SteveMayze/TL2C/doc/web/image/Level-Illuminated-sm.png

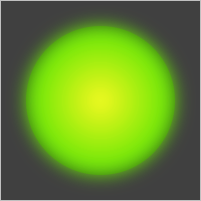
doc/web/image/Level-Illuminated-sm.png
