SteveMayze/TL2C/doc/Connection.png

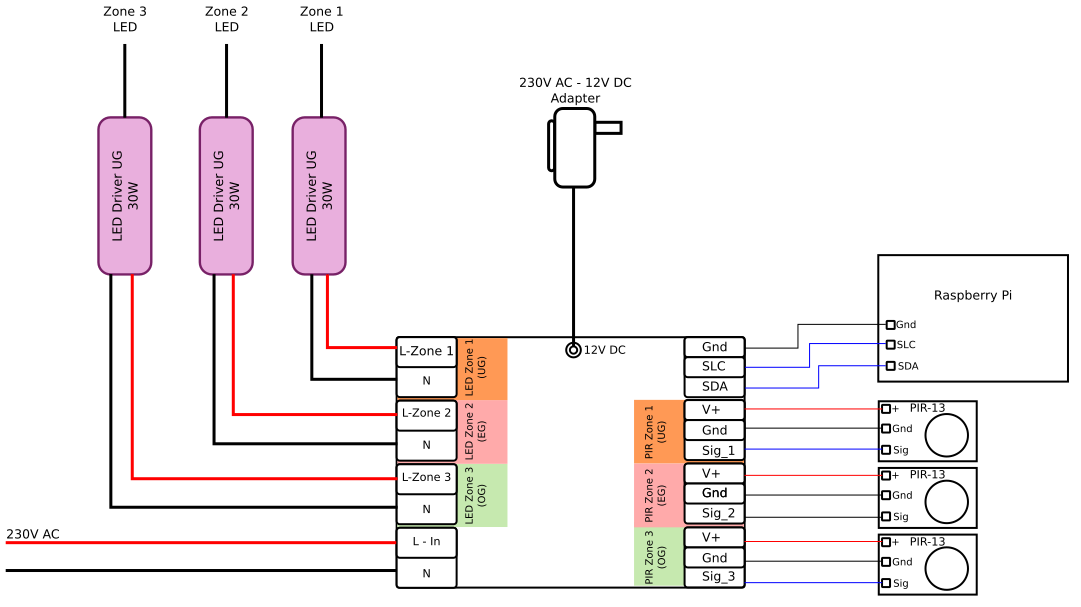
doc/Connection.png
