SteveMayze/TL2C/doc/esp32/CNMB_3_KIT.jpg

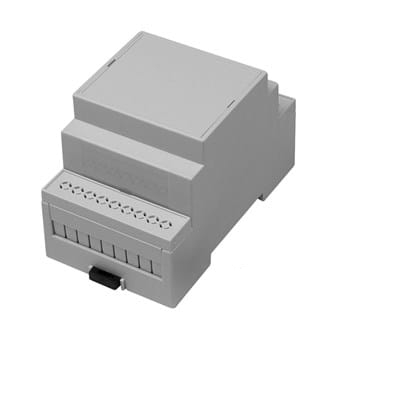
doc/esp32/CNMB_3_KIT.jpg
