SteveMayze/TL2C/doc/esp32/Layout.png

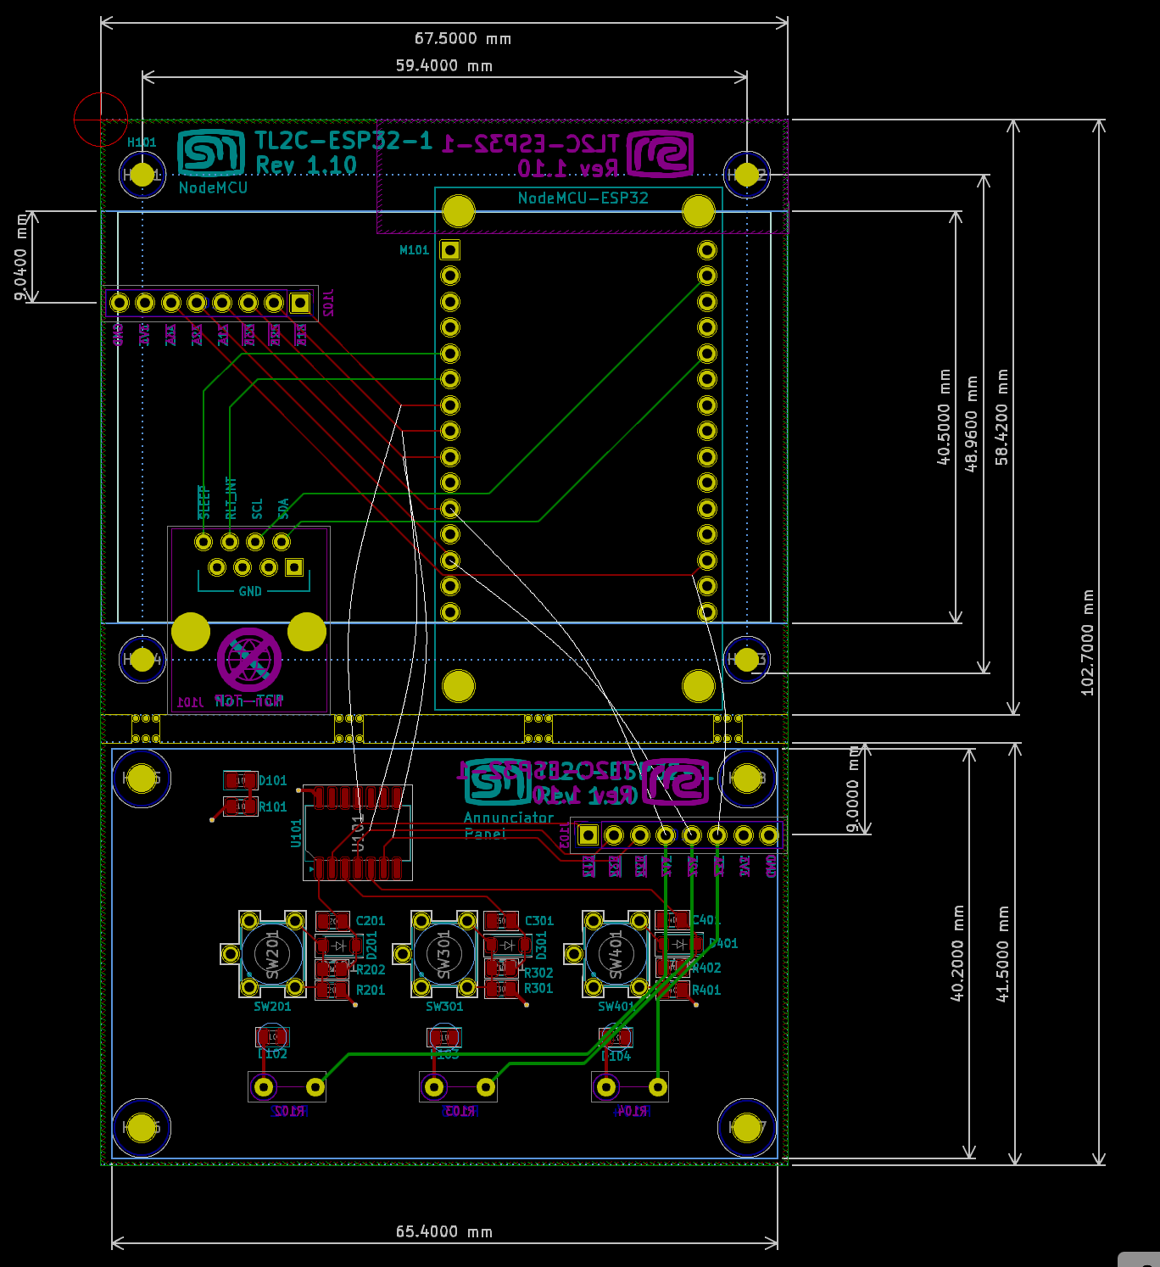
doc/esp32/Layout.png
