SteveMayze/TL2C/doc/esp32/Screenshot 2024-02-02 at 20.17.53.png

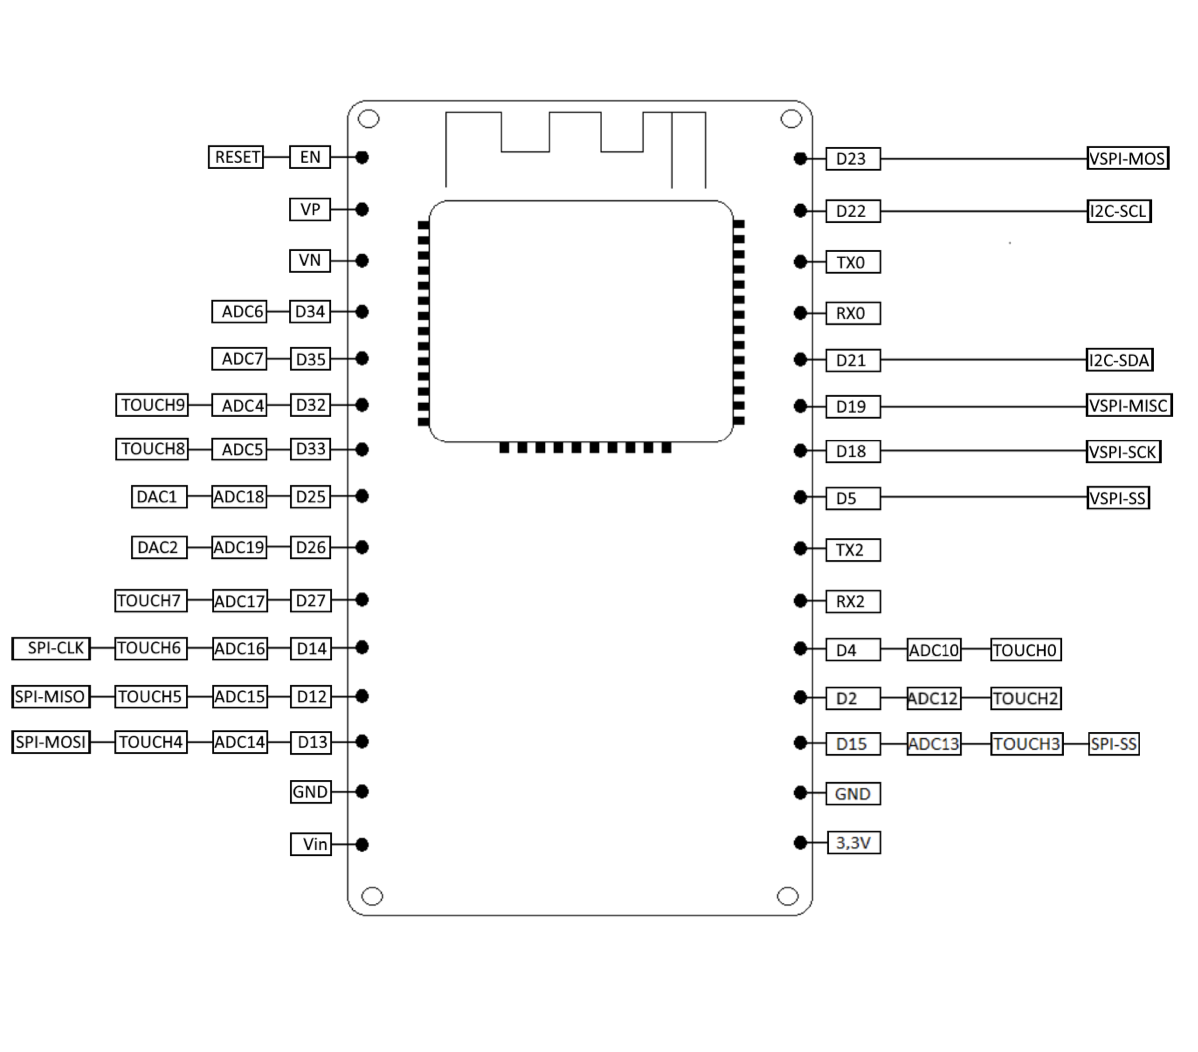
doc/esp32/Screenshot 2024-02-02 at 20.17.53.png
