SteveMayze/TL2C/doc/esp32/Screenshot 2024-02-08 at 13.55.30.png

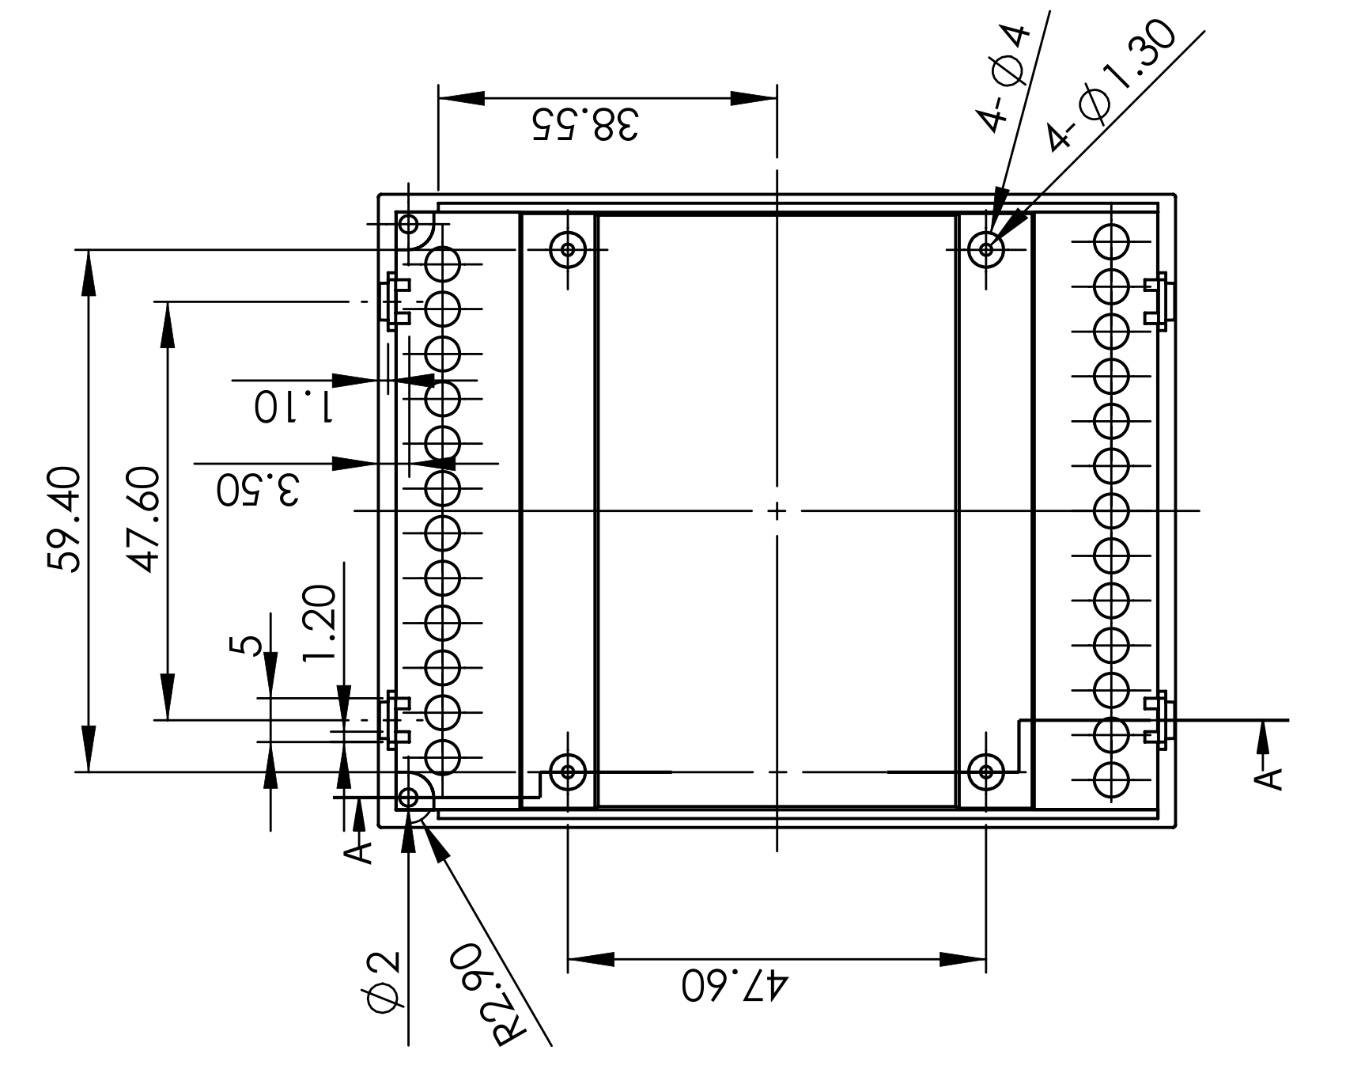
doc/esp32/Screenshot 2024-02-08 at 13.55.30.png
