SteveMayze/TL2C/doc/esp32/Screenshot 2024-03-15 at 17.32.05.png

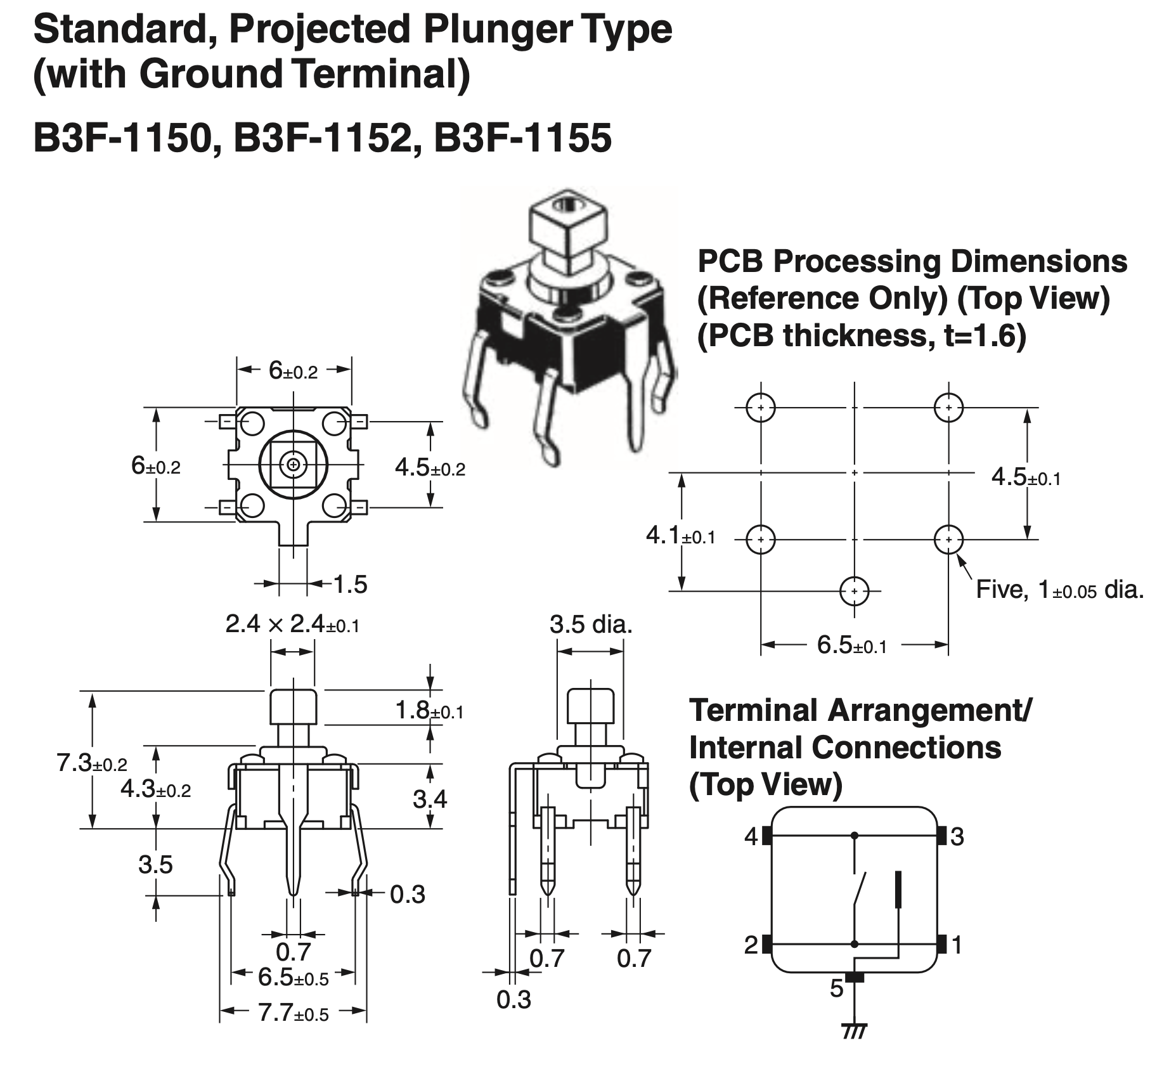
doc/esp32/Screenshot 2024-03-15 at 17.32.05.png
