SteveMayze/TL2C/doc/esp32/Screenshot 2024-03-15 at 17.46.03.png

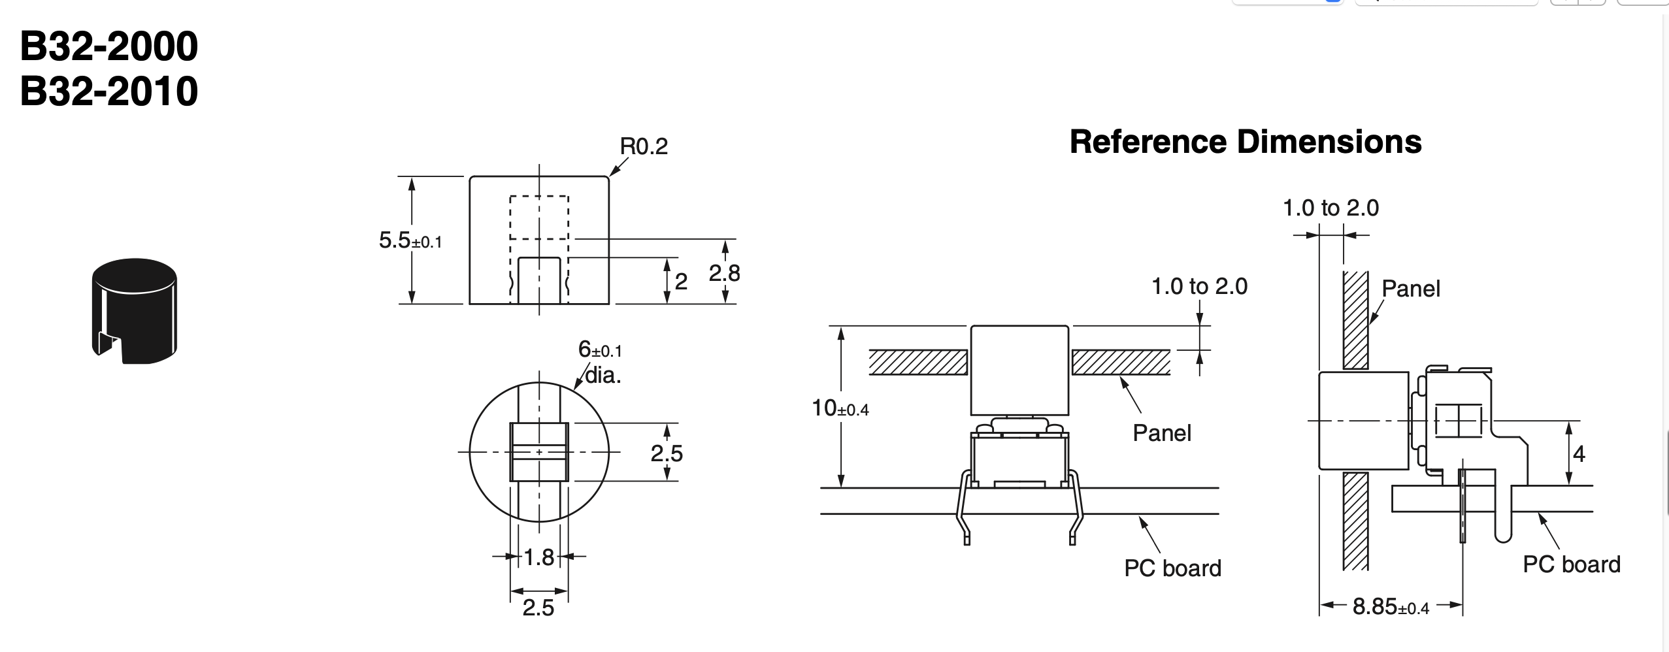
doc/esp32/Screenshot 2024-03-15 at 17.46.03.png
