SteveMayze/TL2C/doc/esp32/tl2c-esp-back.png

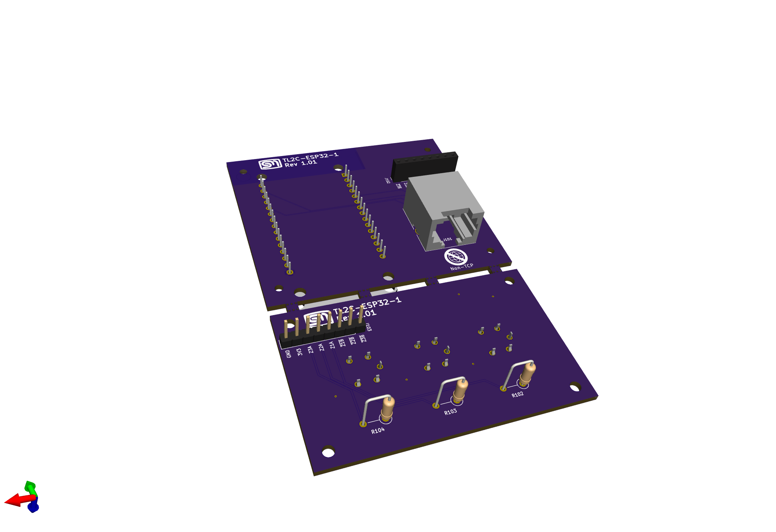
doc/esp32/tl2c-esp-back.png
