SteveMayze/TL2C/doc/esp32/tl2c-esp-front.png

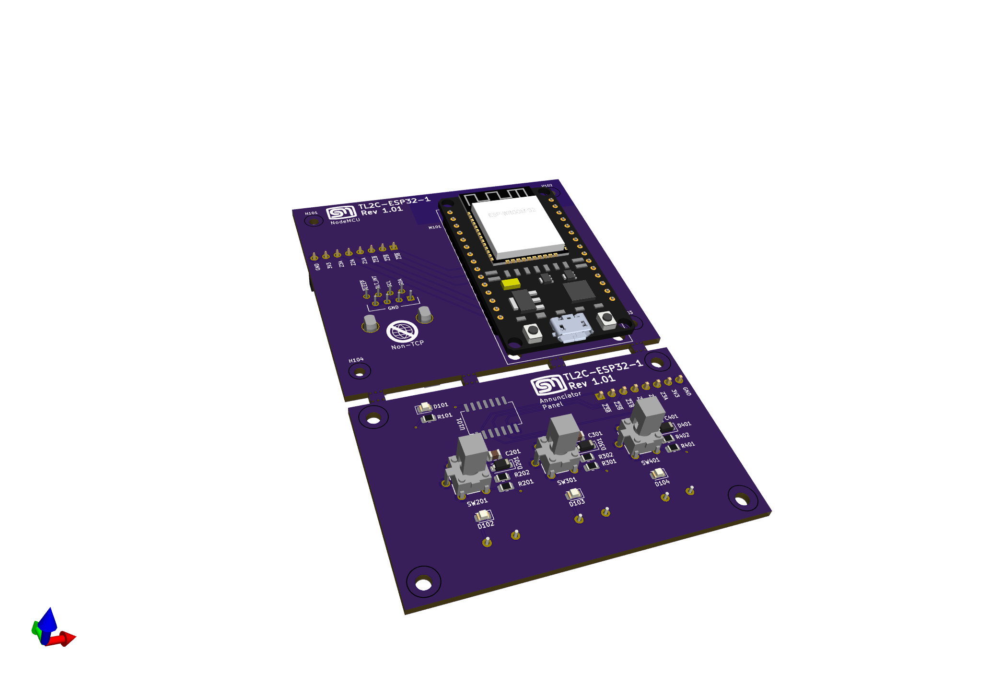
doc/esp32/tl2c-esp-front.png
