SteveMayze/TL2C/doc/esp32/tl2c-register-0.png

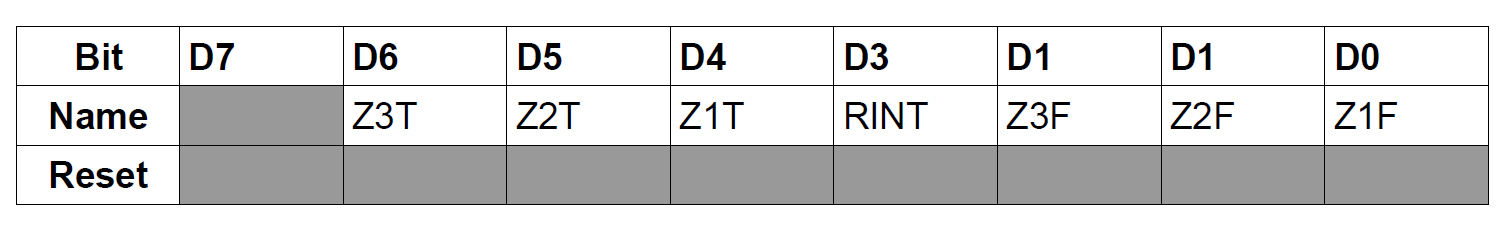
doc/esp32/tl2c-register-0.png
