SteveMayze/TL2C/doc/LED-Driver.png

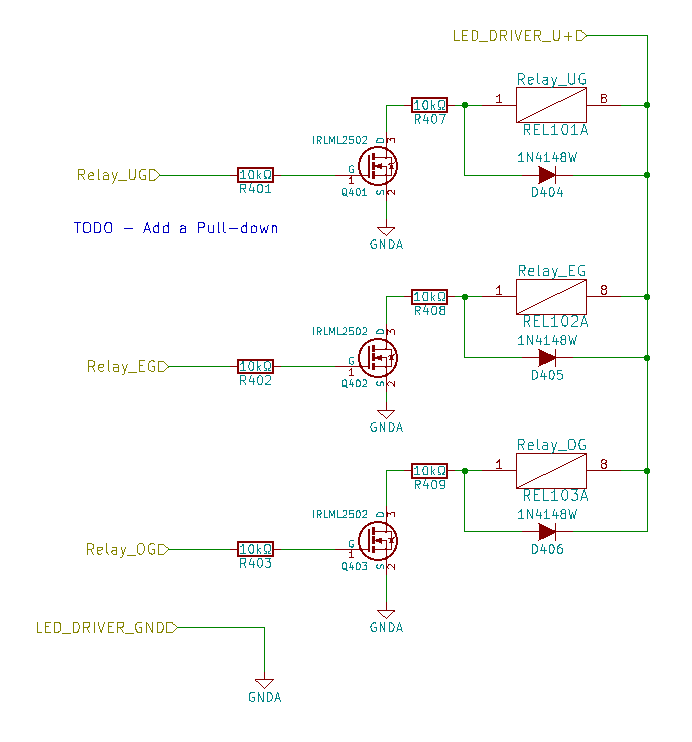
doc/LED-Driver.png
