SteveMayze/TL2C/doc/NewLEDControl.png

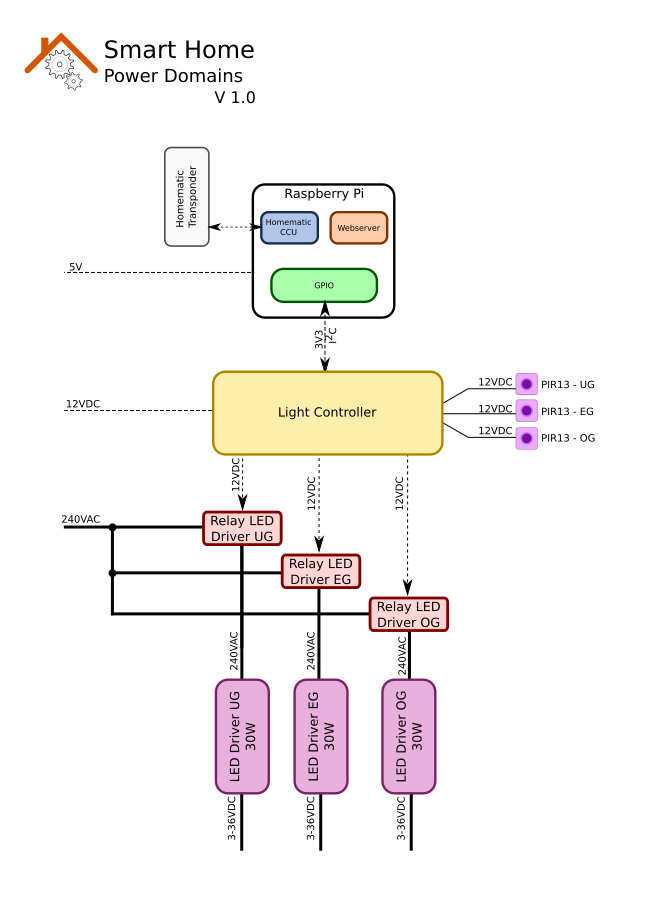
doc/NewLEDControl.png
