SteveMayze/TL2C/doc/tl2c_240v.png

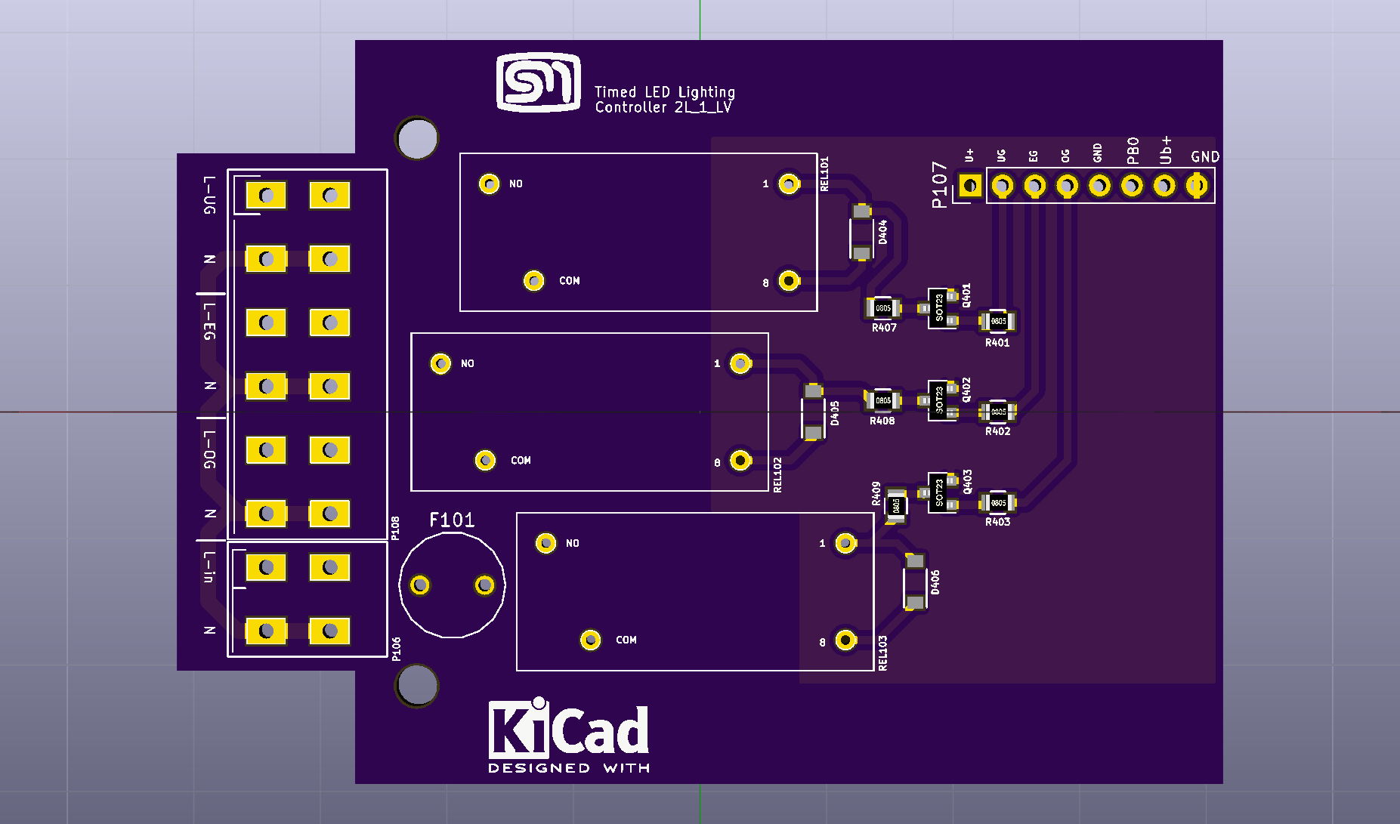
doc/tl2c_240v.png
