SteveMayze/TL2C/doc/tl2c_ctrl.png

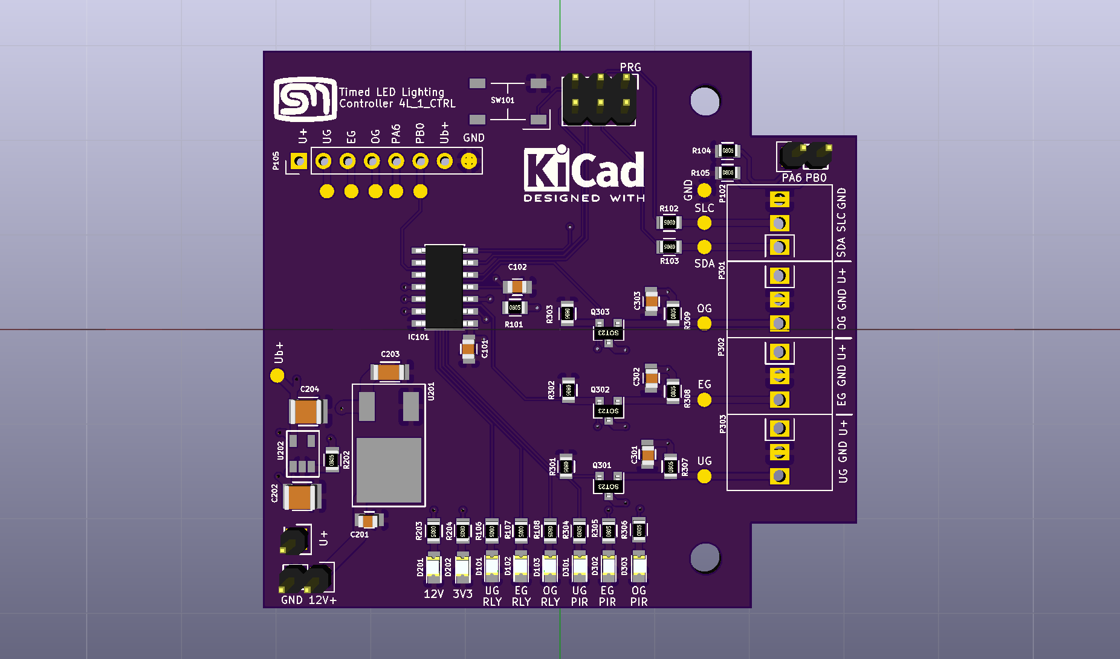
doc/tl2c_ctrl.png
