SteveMayze/TL2C/doc/web/image/Level-Disabled-sm.png

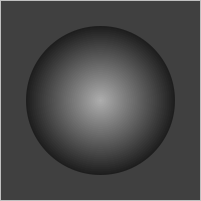
doc/web/image/Level-Disabled-sm.png
