SteveMayze/TL2C/doc/web/image/Level-Enabled-sm.png

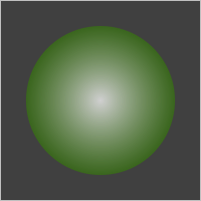
doc/web/image/Level-Enabled-sm.png
