SteveMayze/TL2C/doc/esp32/esp32.pdf

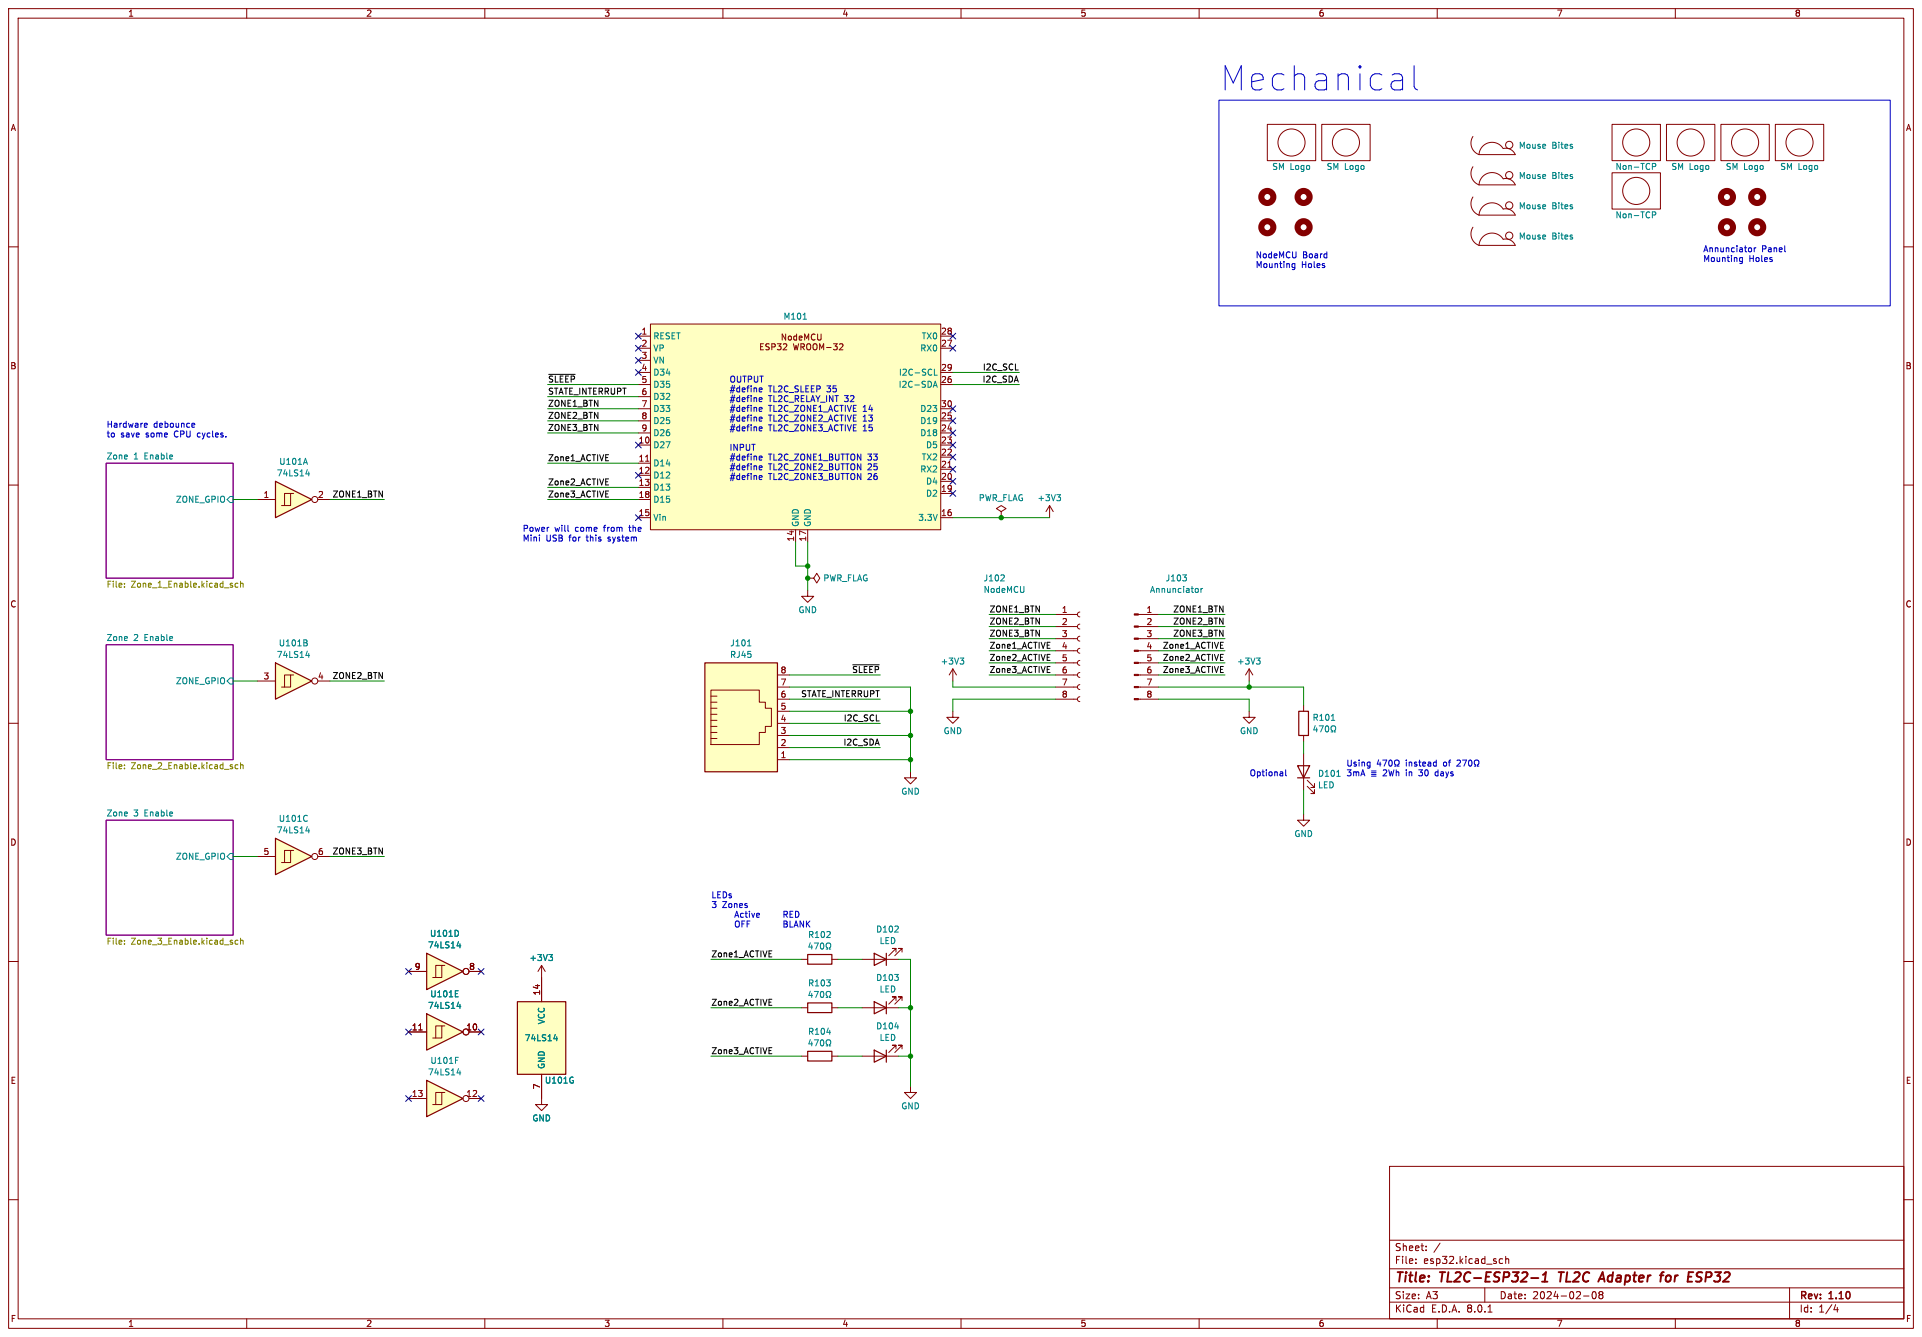
[picture p26: page 1]

SM Logo VCC 14 GND

#define TL2C_ZONE3_BUTTON 26 Hardware debounce
to save some CPU cycles.

Power will come from the Mini USB for this system

LEDs 3 Zones Active RED OFF BLANK

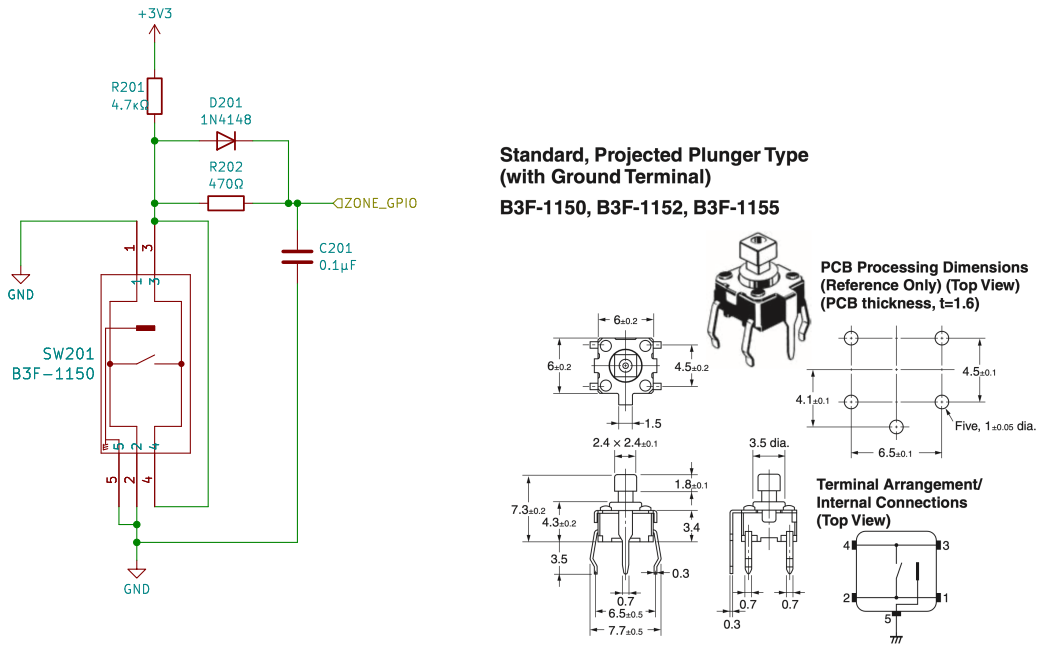
[picture p27: page 2]

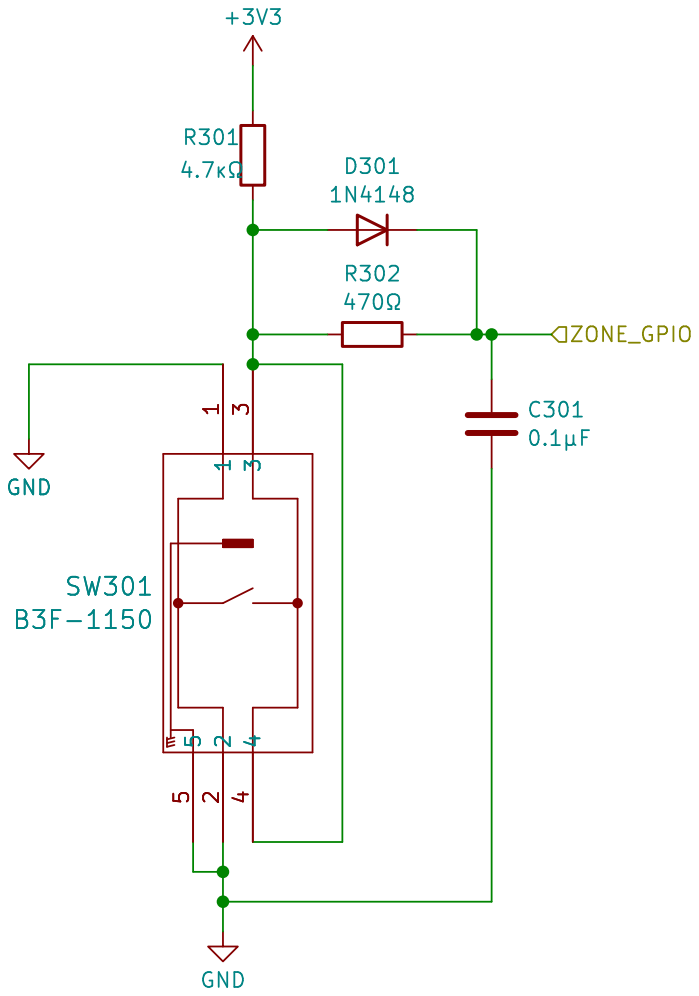
[picture p28: page 3]

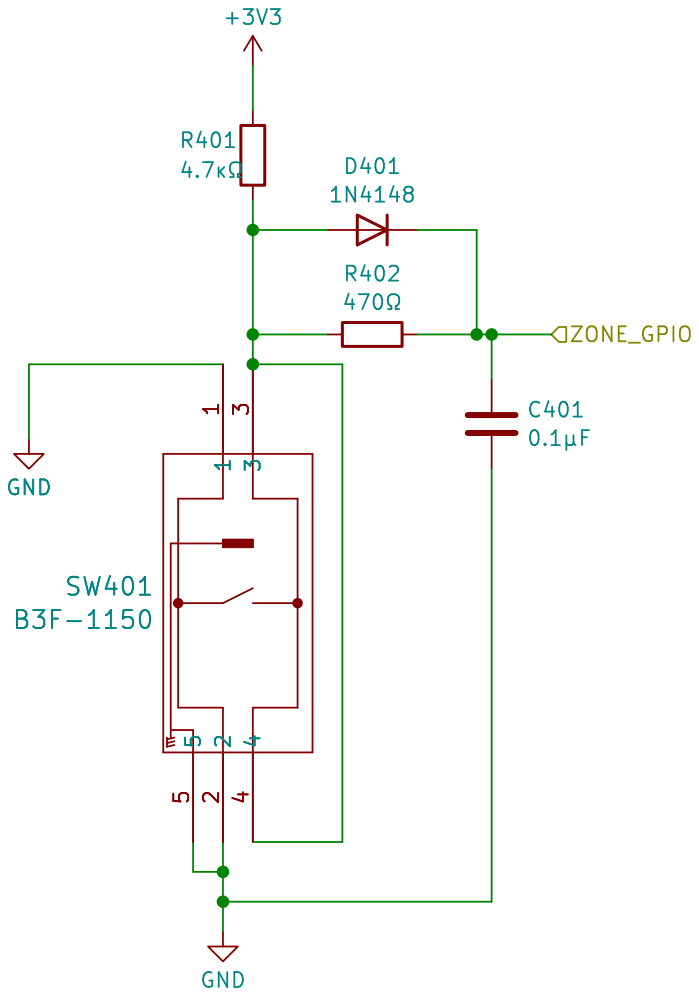
[picture p29: page 4]
