SteveMayze/TL2C/doc/esp32/tl2c-esp32.pdf

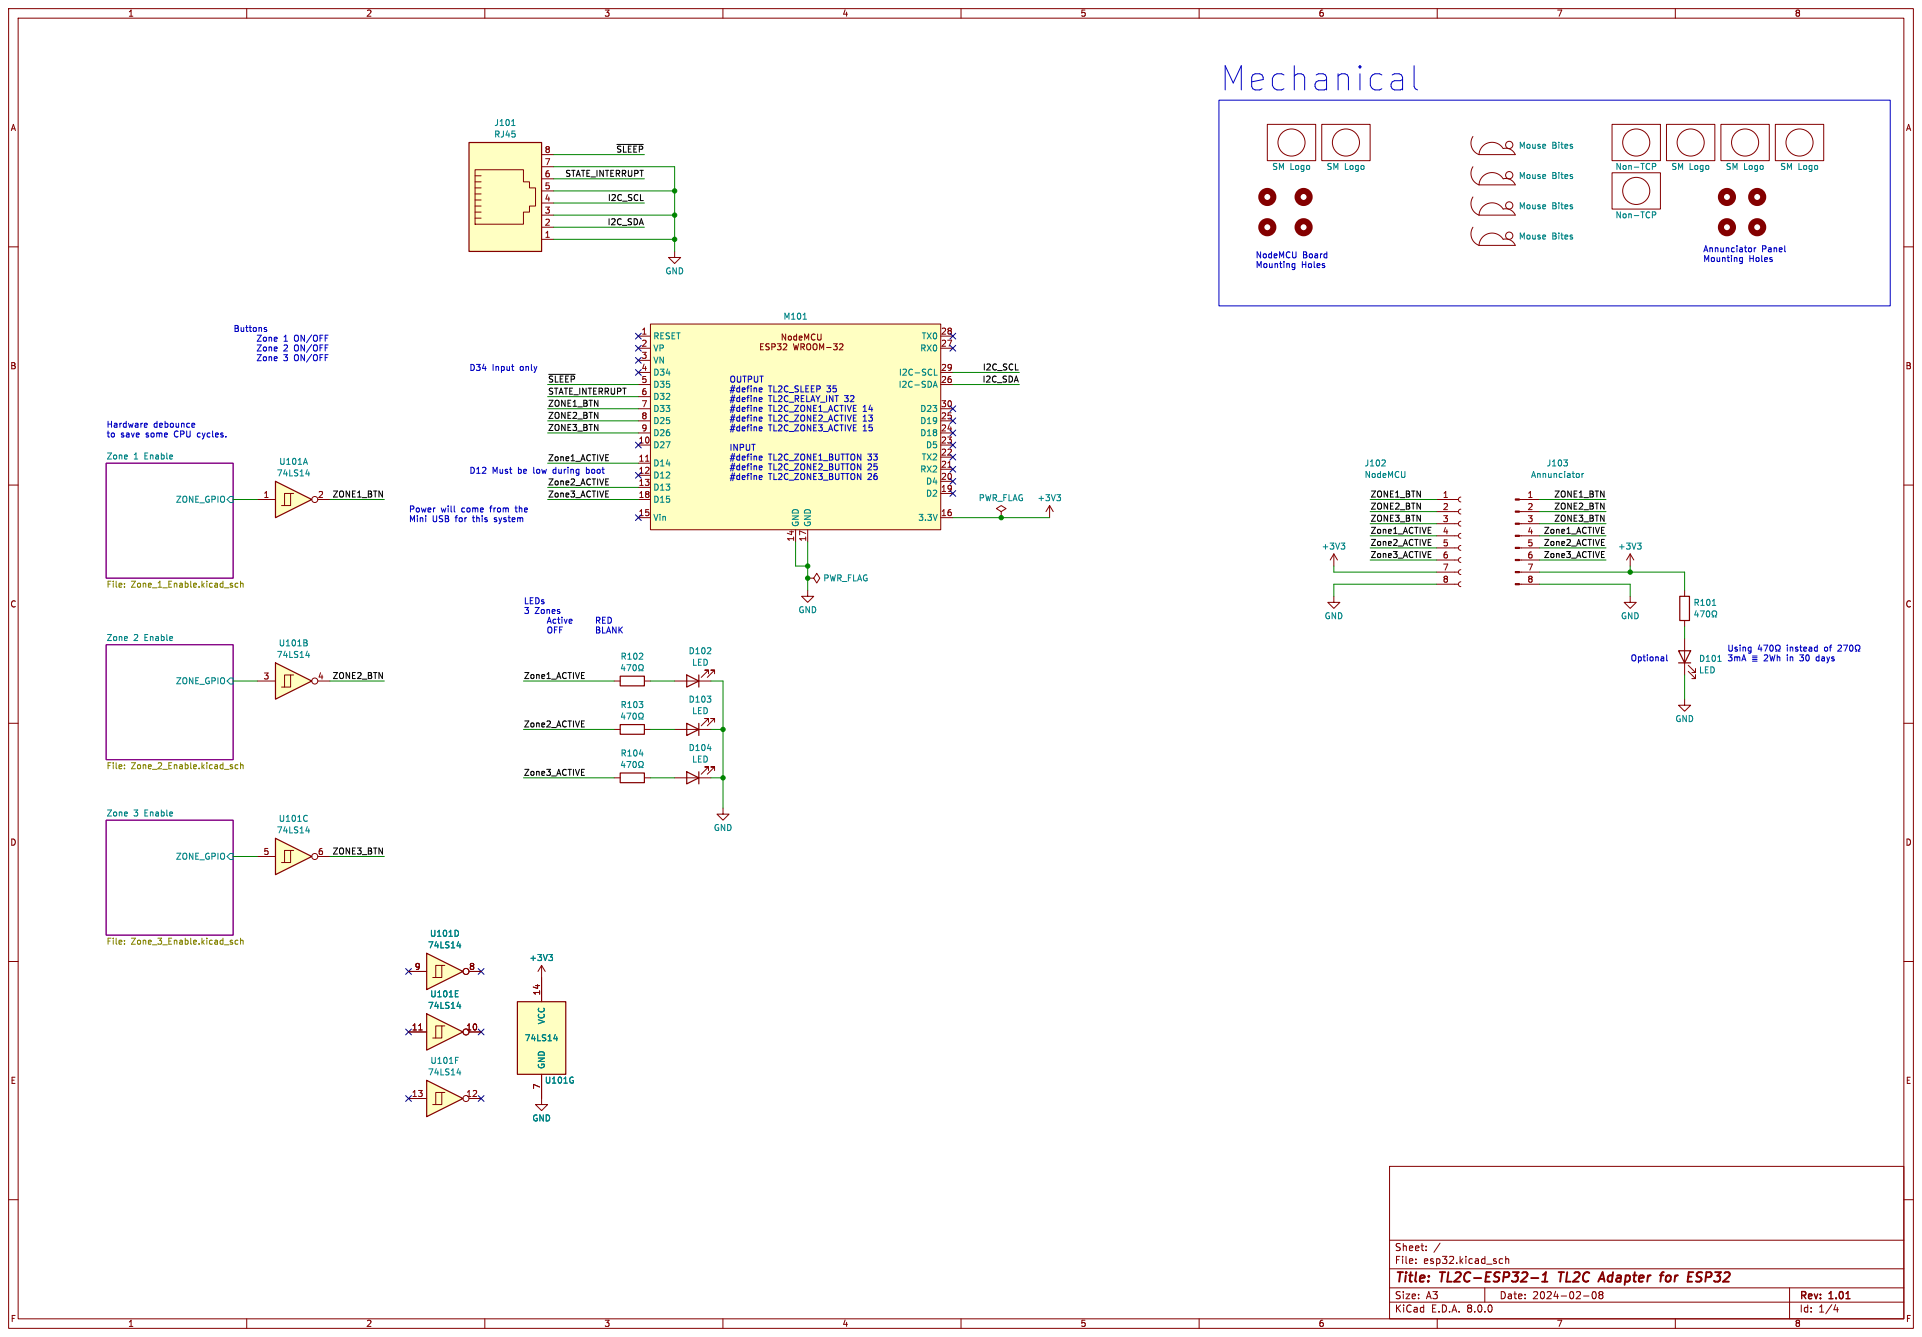
[picture p30: page 1]

Mouse Bites SM Logo R104

3mA þÿ"c2Wh in 30 days D12 Must be low during boot Power will come from the Mini USB for this system

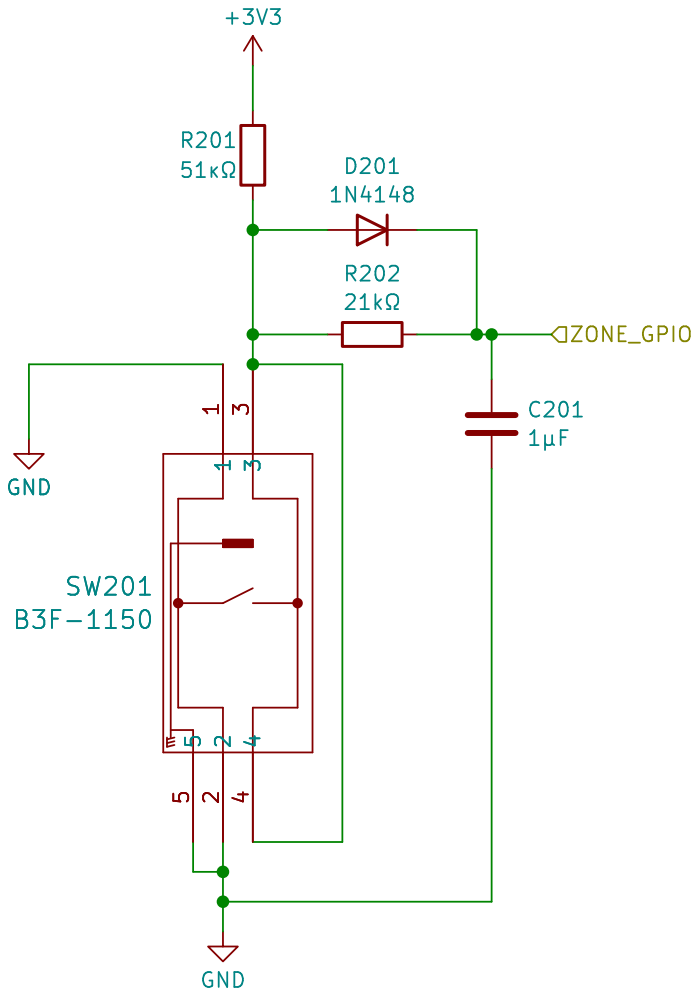
[picture p31: page 2]

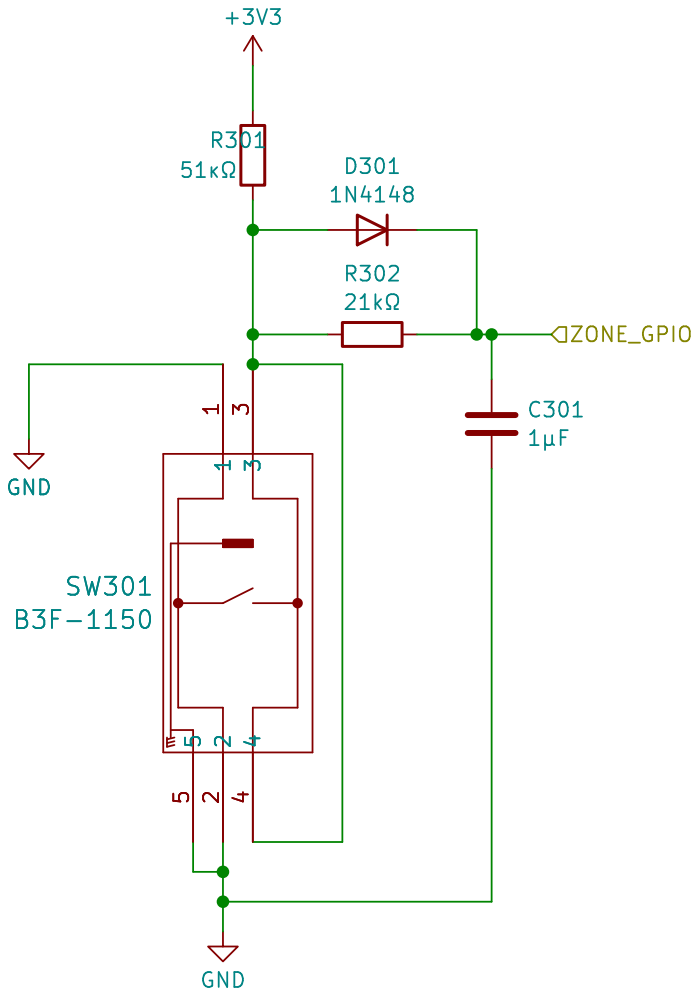
[picture p32: page 3]

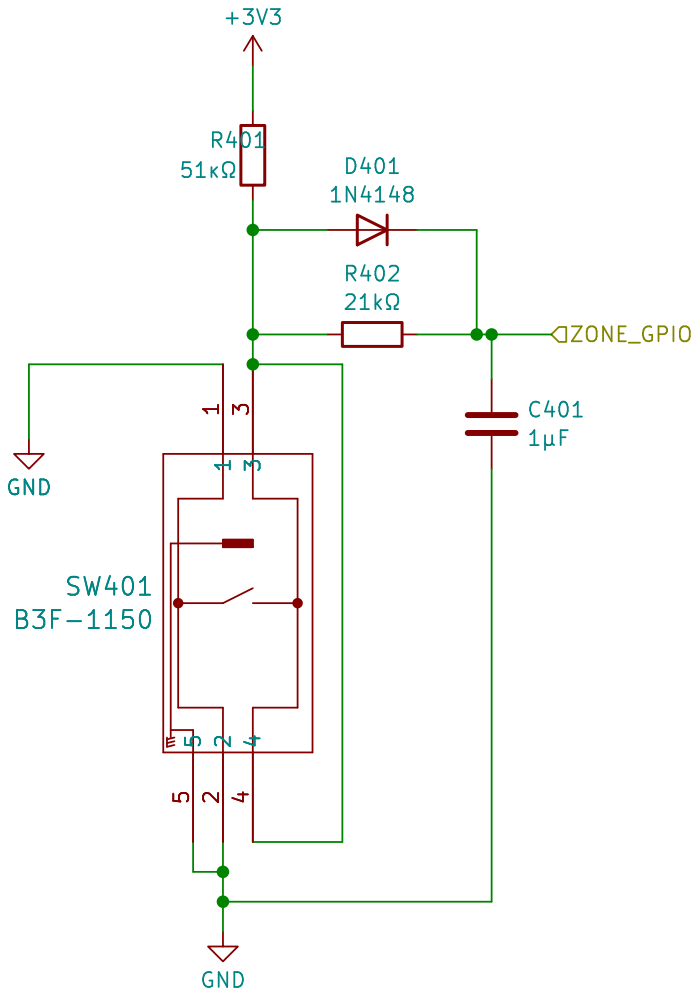
[picture p33: page 4]
