SteveMayze/TL2C/doc/esp32/esp32-B_Cu.pdf

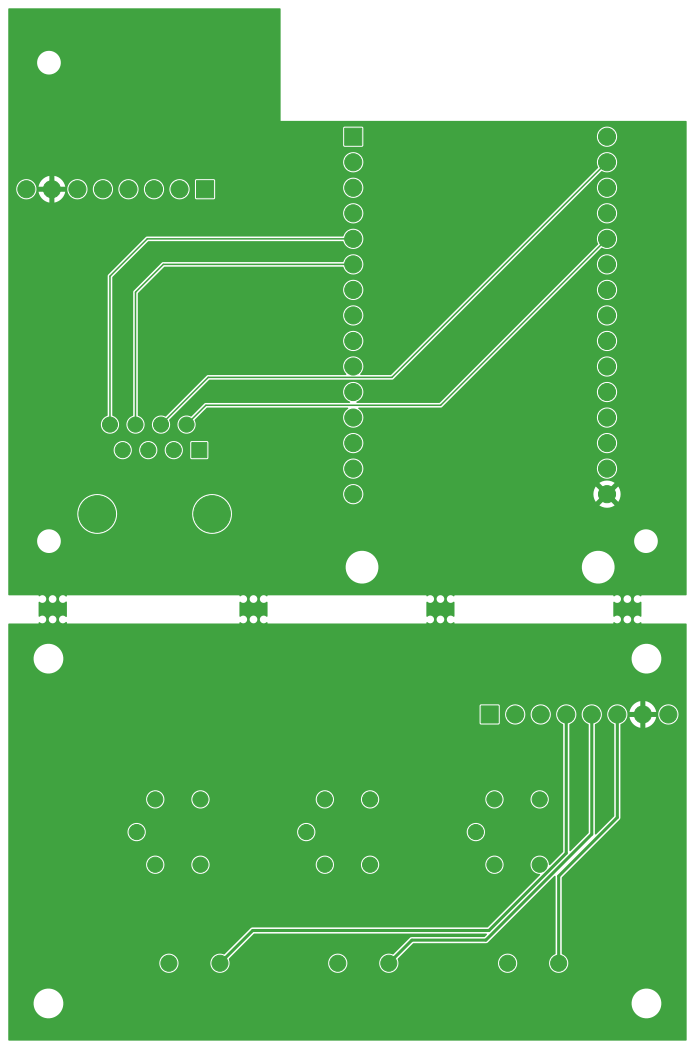
[picture p44: page 1]
