SteveMayze/TL2C/doc/esp32/esp32-B_Mask.pdf

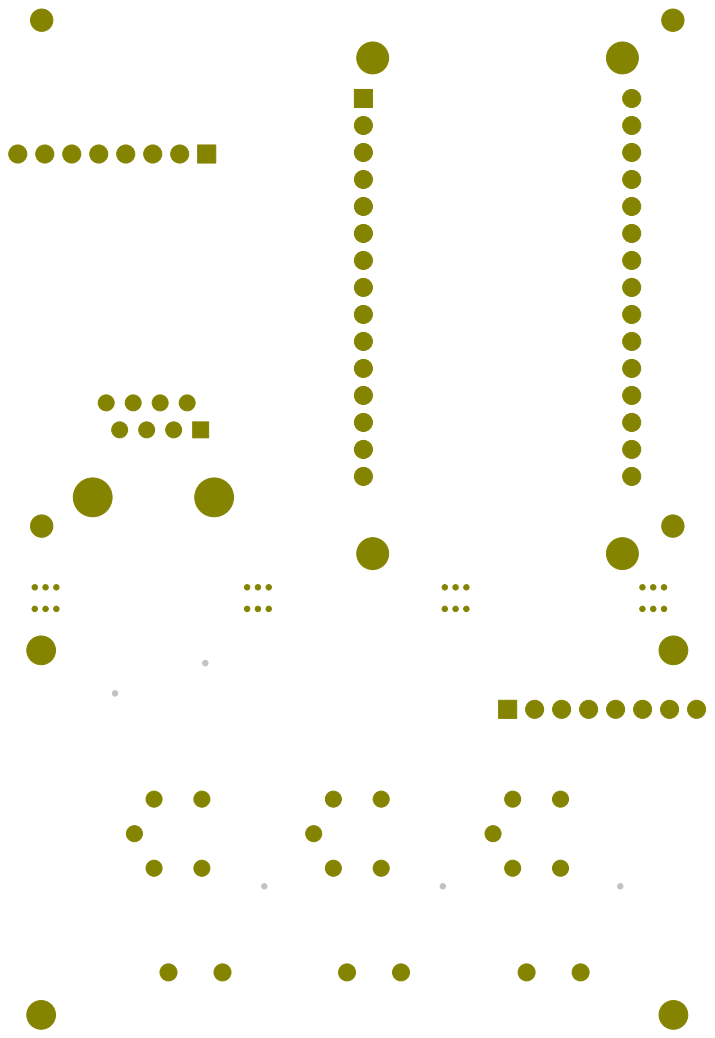
[picture p45: page 1]
