SteveMayze/TL2C/doc/esp32/esp32-B_Silkscreen.pdf

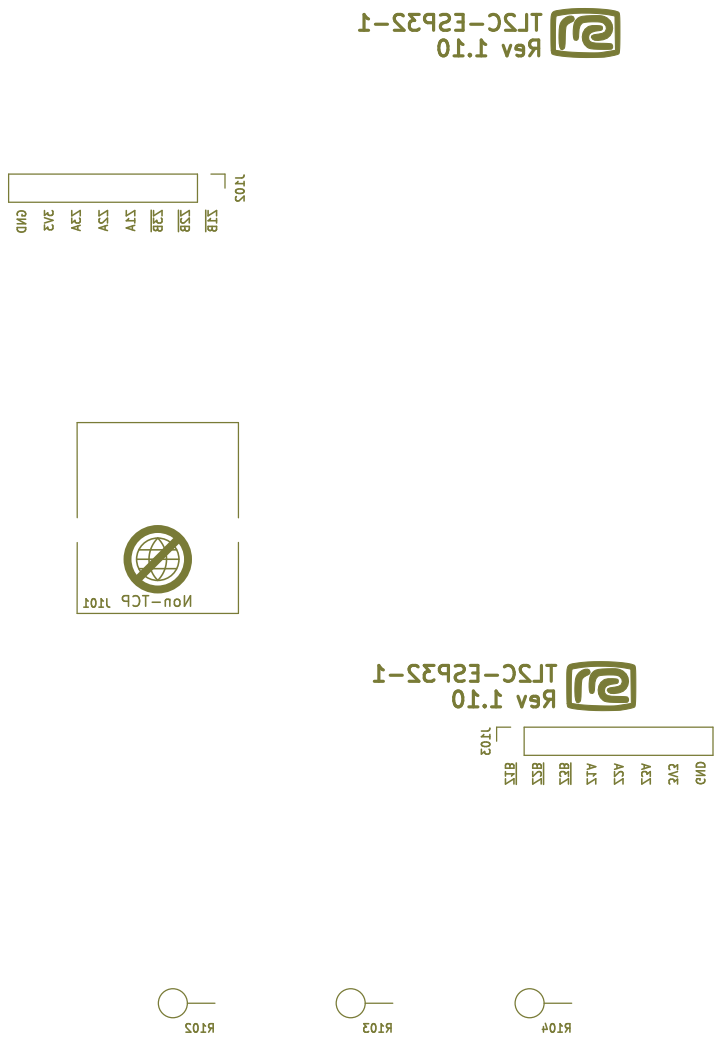
[picture p46: page 1]
