SteveMayze/TL2C/doc/esp32/esp32-Edge_Cuts.pdf

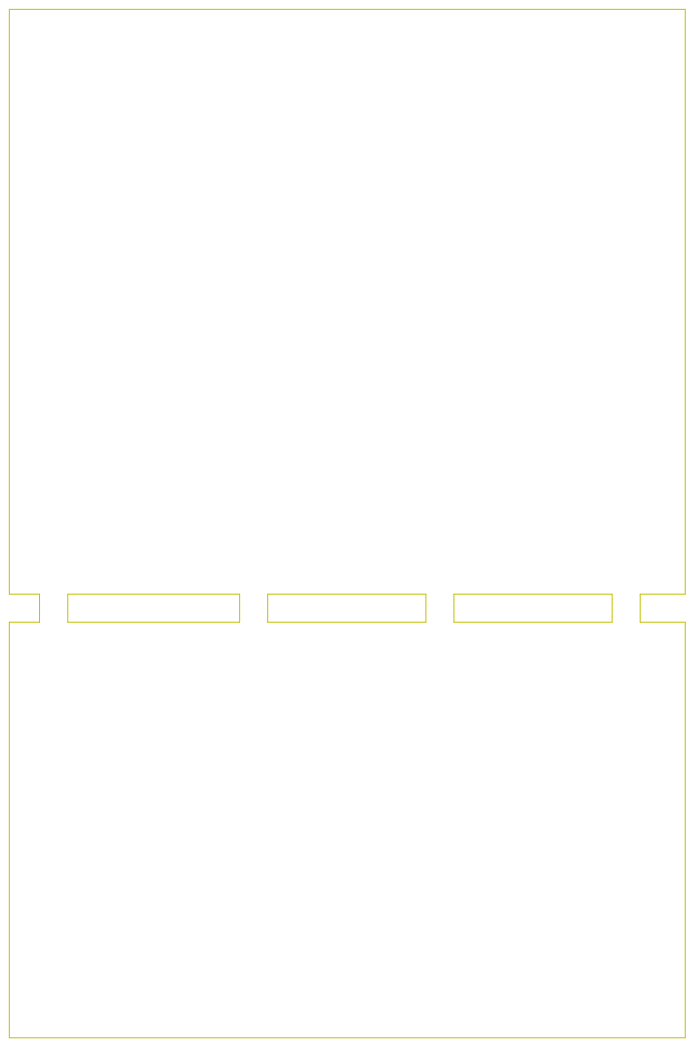
[picture p47: page 1]
