SteveMayze/TL2C/doc/esp32/esp32-F_Cu.pdf

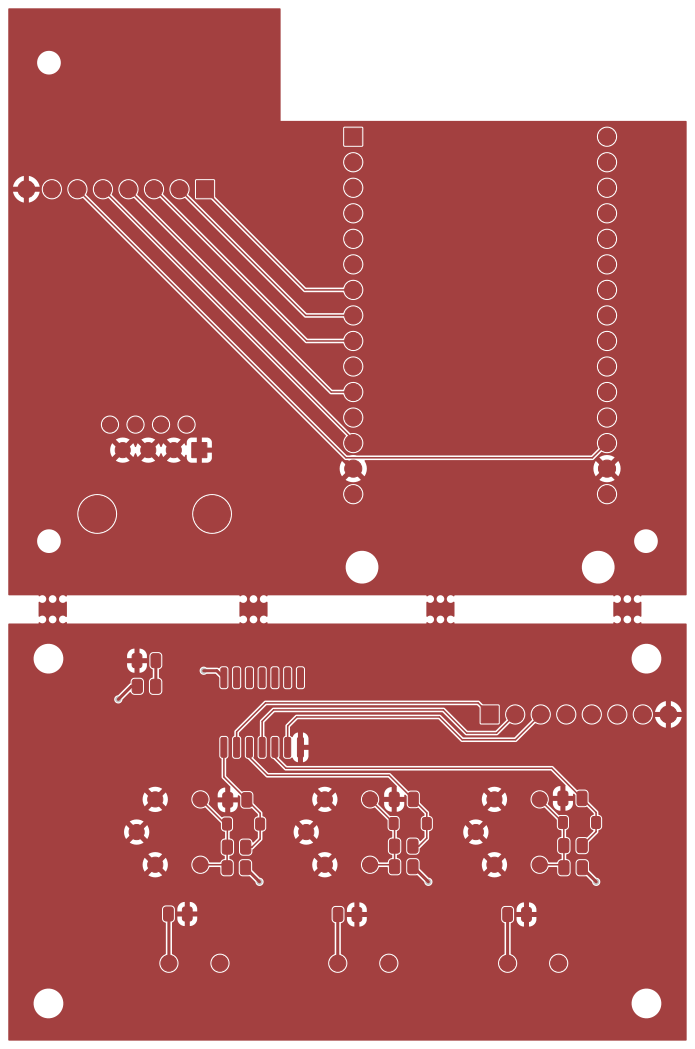
[picture p48: page 1]
