SteveMayze/TL2C/doc/esp32/esp32-F_Mask.pdf

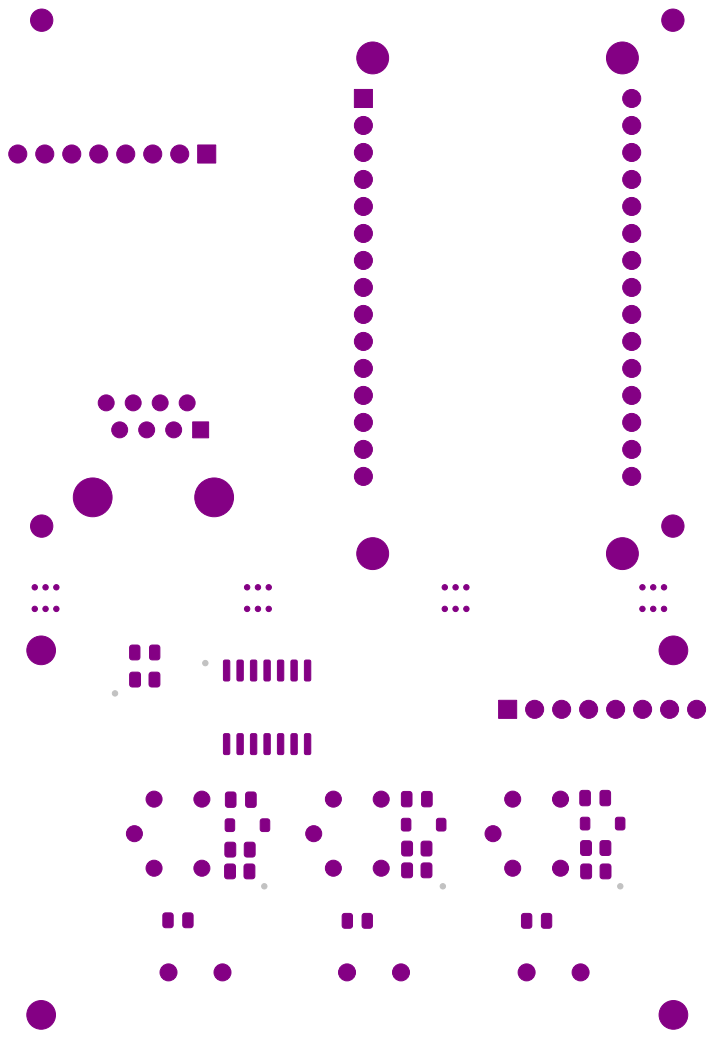
[picture p49: page 1]
