SteveMayze/TL2C/doc/esp32/esp32-F_Paste.pdf

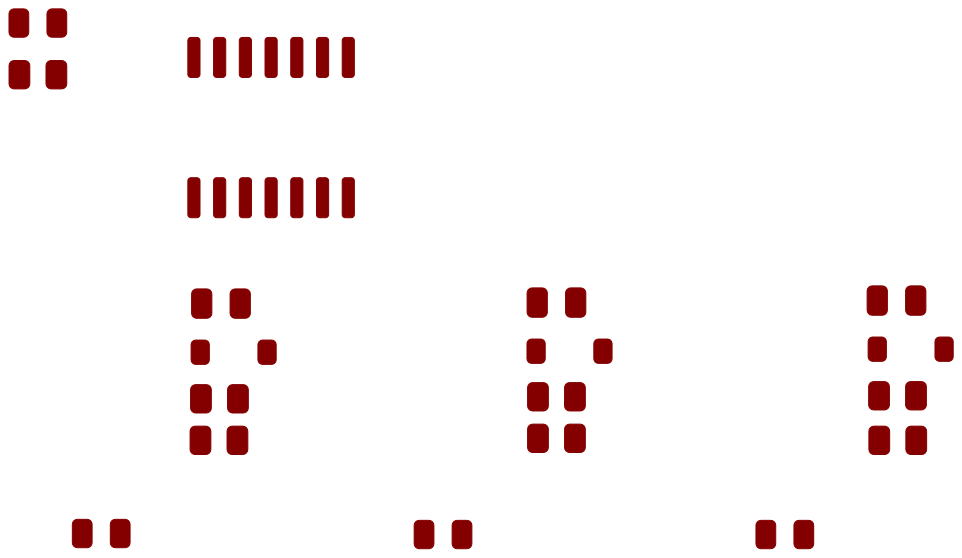
[picture p50: page 1]
