SteveMayze/TL2C/doc/esp32/esp32-F_Silkscreen.pdf

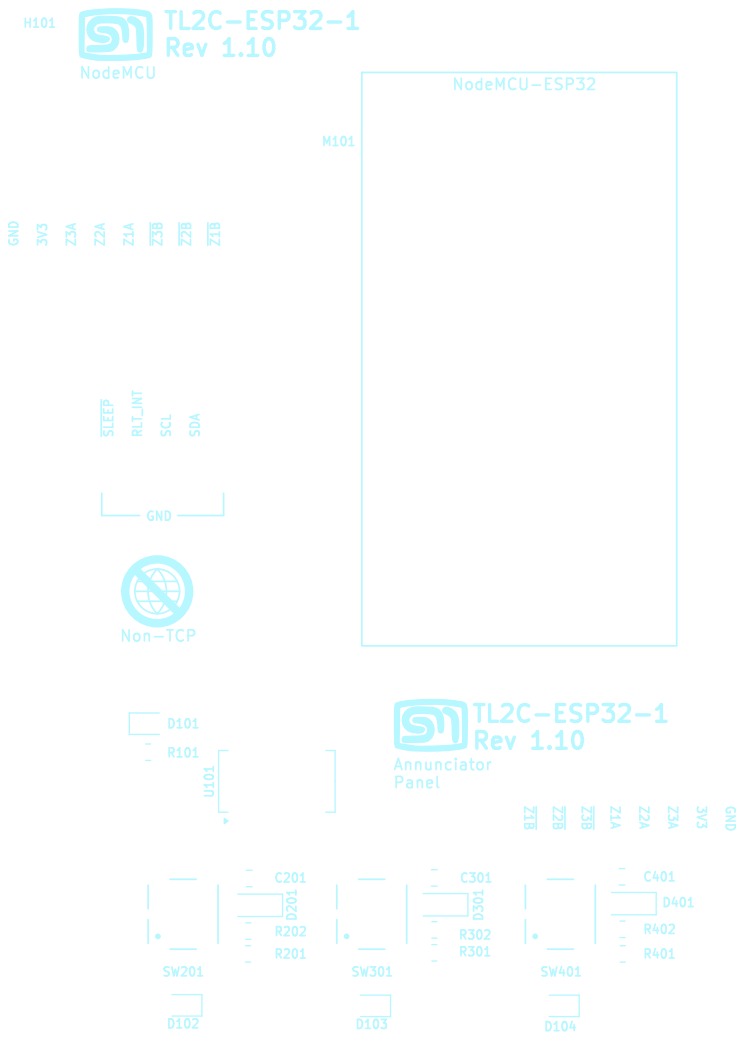
[picture p51: page 1]
