SteveMayze/TL2C/doc/esp32/FrontPanel-Artwork.pdf

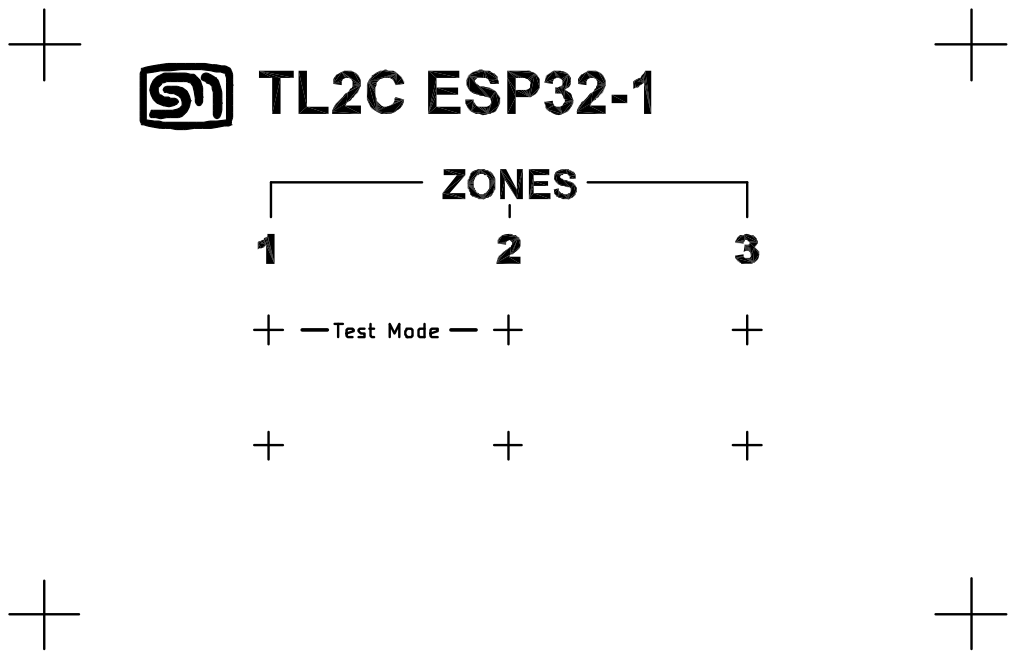
[picture p52: page 1]
