SteveMayze/TL2C/doc/esp32/Label-Artwork.pdf

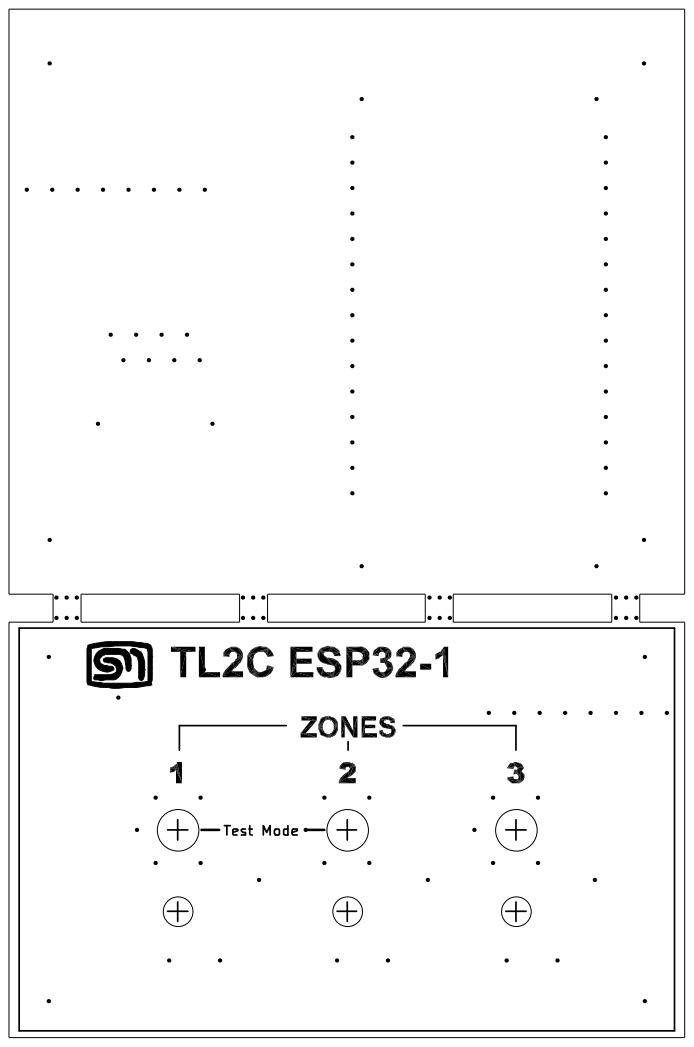
[picture p53: page 1]
