SteveMayze/TL2C/doc/esp32/datenblatt-1401749-fci-modular-jacks-rj45-einbaubuchse-54601-908wplf-buchse-einbau-horizontal-pole-8p8c-schwarz-1-st.pdf

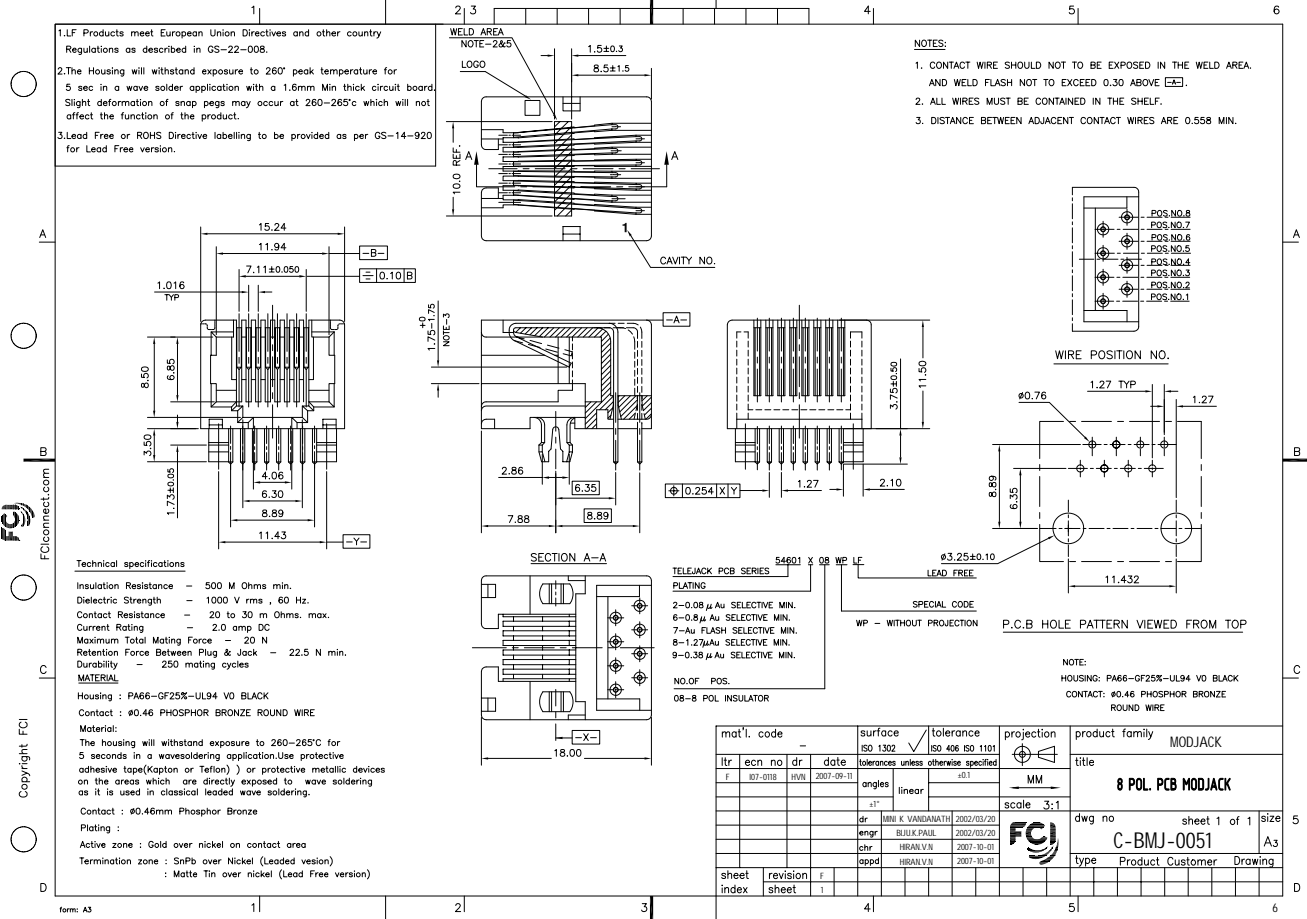
[picture p54: page 1]

±1°
MINI K VANDANATH | | 2002/03/20
BIJU.K.PAUL | 2002/03/20
HIRAN.V.N | 2007-10-01
