SteveMayze/TL2C/firmware/tl2c/tl2c/TWI_slave.h

/*
 * twi_slave.h
 *
 * Created: 18/02/2017 15:26:52
 * Author : Steve
 */ 

 #ifndef __twi_slave_h__
 #define __twi_slave_h__

 #define TWI_BUFFER_SIZE 5
 #define red_LED 0x00
 #define yellow_LED 0x01
 #define green_LED 0x02



 /**
	The structure that models the TWI status register.
  */
 union TWI_statusReg_A_t {
	 unsigned char all;
	 struct {
		 unsigned char TWI_TWAS:1;		// TWI Address or Stop 
		 unsigned char TWI_TWDIR:1;		// TWI Read/Write Direction 
		 unsigned char TWI_TWBE:1;		// TWI Bus Error
		 unsigned char TWI_TWC:1;		// TWI Collision
		 unsigned char TWI_TWRA:1;		// TWI Receive Acknowledge
		 unsigned char TWI_TWCH:1;		// TWI Clock Hold
 		 unsigned char TWI_TWASIF:1;	// TWI Address/Stop Interrupt Flag
		 unsigned char TWI_TWDIF:1;		// TWI Data Interrupt Flag
	 };
 };

volatile union TWI_statusReg_A_t TWI_statusReg_A;
volatile unsigned char TWI_Buffer[TWI_BUFFER_SIZE];
volatile unsigned char twi_buffer_idx;

volatile unsigned int led_flag;

unsigned char TWI_Slave_Initialise( unsigned char TWI_ownAddress );
unsigned char TWI_Start(void);
unsigned char TWI_isBusy(void);

#define TWI_NO_STATE               0xF8  // No relevant state information available;

#endif
